janakj/g-1000dxc/kicad/g-1000dxc.kicad_sch

## KiCad design kicad/g-1000dxc.kicad_sch (2022-08-14)

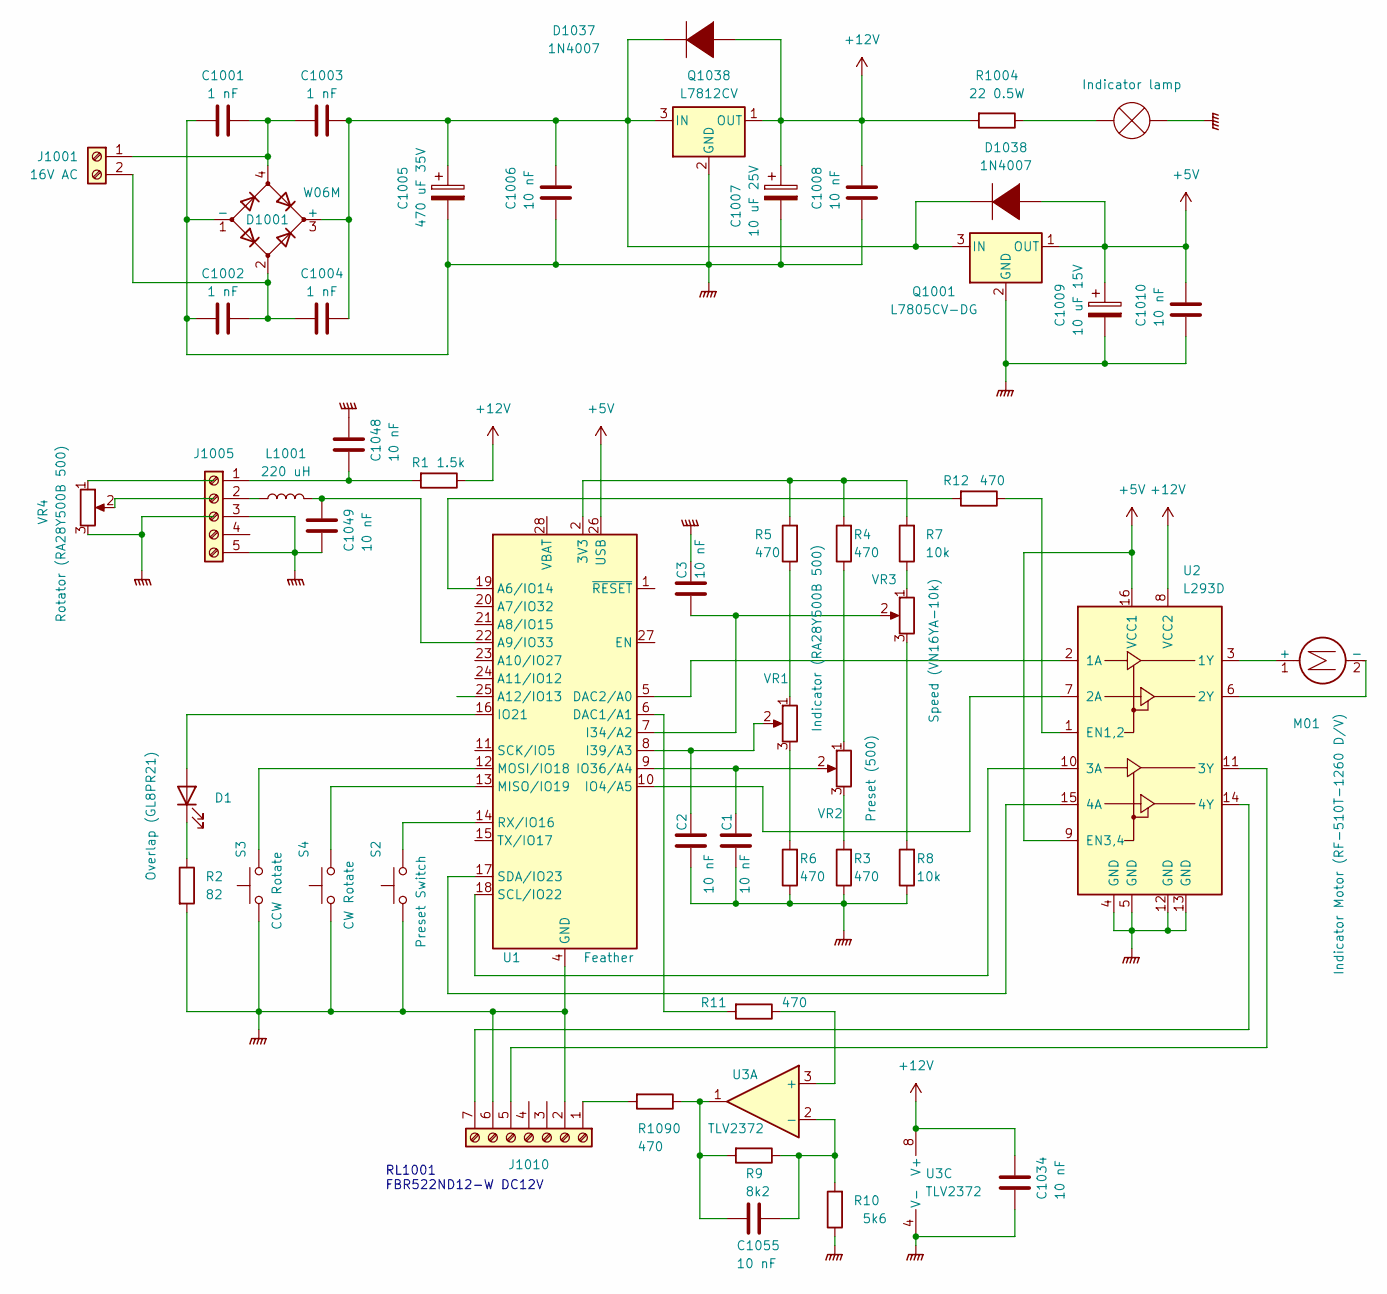
[picture p10: schematic g-1000dxc.kicad_sch]

Parts:
C1, C2, C3, C1006, C1008, C1010, C1034, C1048, C1049, C1055: 10 nF
C1001, C1002, C1003, C1004: 1 nF
C1005: 470 uF 35V
C1007: 10 uF 25V
C1009: 10 uF 15V
D1: Overlap (GL8PR21)
D1001: W06M
D1037, D1038: 1N4007
J1001: 16V AC
J1005: Screw_Terminal_01x05
J1010: Screw_Terminal_01x07
L1001: 220 uH
M01: Indicator Motor (RF-510T-1260 D/V)
Q1001: L7805CV-DG; TO-92_Inline
Q1038: L7812CV; TO-92_Inline
R1: 1.5k
R2: 82
R3, R4, R5, R6, R11, R12, R1090: 470
R7, R8: 10k
R9: 8k2
R10: 5k6
R1004: 22 0.5W
S2: Preset Switch
S3: CCW Rotate
S4: CW Rotate
U1: Feather; Adafruit_Feather
U2: L293D; DIP-16_W7.62mm
U3: TLV2372
VR1: Indicator (RA28Y500B 500)
VR2: Preset (500)
VR3: Speed (VN16YA-10k)
VR4: Rotator (RA28Y500B 500)

Connections:
unnamed: C1.1, C2.1, R3.1, R6.1, R8.1
unnamed: C1.2, U1.9 (IO36/A4), VR2.2
unnamed: C2.2, U1.8 (I39/A3), VR1.2
unnamed: C3.1, U1.7 (I34/A2), VR3.2
unnamed: C1001.1, C1002.1, C1005.2, C1006.1, C1007.2, C1008.1, D1001.1 (-), Q1038.2 (GND)
unnamed: C1001.2, C1003.1, D1001.4, J1001.1
unnamed: C1002.2, C1004.1, D1001.2, J1001.2
unnamed: C1003.2, C1004.2, C1005.1, C1006.2, D1001.3 (+), D1037.2 (A), D1038.2 (A), Q1001.3 (VI), Q1038.3 (VI)
unnamed: C1007.1, C1008.2, D1037.1 (K), Q1038.1 (VO), R1004.2
unnamed: C1009.1, C1010.2, D1038.1 (K), Q1001.1 (VO)
unnamed: C1009.2, C1010.1, Q1001.2 (GND)
unnamed: C1034.1, U3.4 (V-)
unnamed: C1034.2, U3.8 (V+)
unnamed: C1048.1, J1005.1, R1.2
unnamed: C1049.1, J1005.3, J1005.5
unnamed: C1049.2, L1001.2, U1.22 (A9/IO33)
unnamed: C1055.1, R9.2, R1090.1, U3.1
unnamed: C1055.2, R9.1, R10.2, U3.2 (-)
unnamed: D1.1 (K), R2.1
unnamed: D1.2 (A), U1.16 (IO21)
unnamed: J1005.2, L1001.1
unnamed: J1010.1, R1090.2
unnamed: J1010.2, J1010.6, R2.2, S2.1, S3.1, S4.1, U1.4 (GND)
unnamed: J1010.5, U2.11 (3Y)
unnamed: J1010.7, U2.14 (4Y)
unnamed: M01.1 (+), U2.3 (1Y)
unnamed: M01.2 (-), U2.6 (2Y)
unnamed: R3.2, VR2.3
unnamed: R4.1, VR2.1
unnamed: R4.2, R5.2, R7.2, U1.2 (3V3)
unnamed: R5.1, VR1.1
unnamed: R6.2, VR1.3
unnamed: R7.1, VR3.1
unnamed: R8.2, VR3.3
unnamed: R11.1, U3.3 (+)
unnamed: R11.2, U1.6 (DAC1/A1)
unnamed: R12.1, U2.1 (EN1,2)
unnamed: R12.2, U1.19 (A6/IO14)
unnamed: S2.2, U1.14 (RX/IO16)
unnamed: S3.2, U1.12 (MOSI/IO18)
unnamed: S4.2, U1.13 (MISO/IO19)
unnamed: U1.5 (DAC2/A0), U2.2 (1A)
unnamed: U1.10 (IO4/A5), U2.7 (2A)
unnamed: U1.17 (SDA/IO23), U2.15 (4A)
unnamed: U1.18 (SCL/IO22), U2.10 (3A)
unnamed: U2.4 (GND), U2.5 (GND), U2.12 (GND), U2.13 (GND)
unnamed: U2.9 (EN3,4), U2.16 (VCC1)

Notes on the sheet:
RL1001 FBR522ND12-W DC12V
